Dylancyclone/thesis/defense/images/chrome_coo2XuAIJX.png

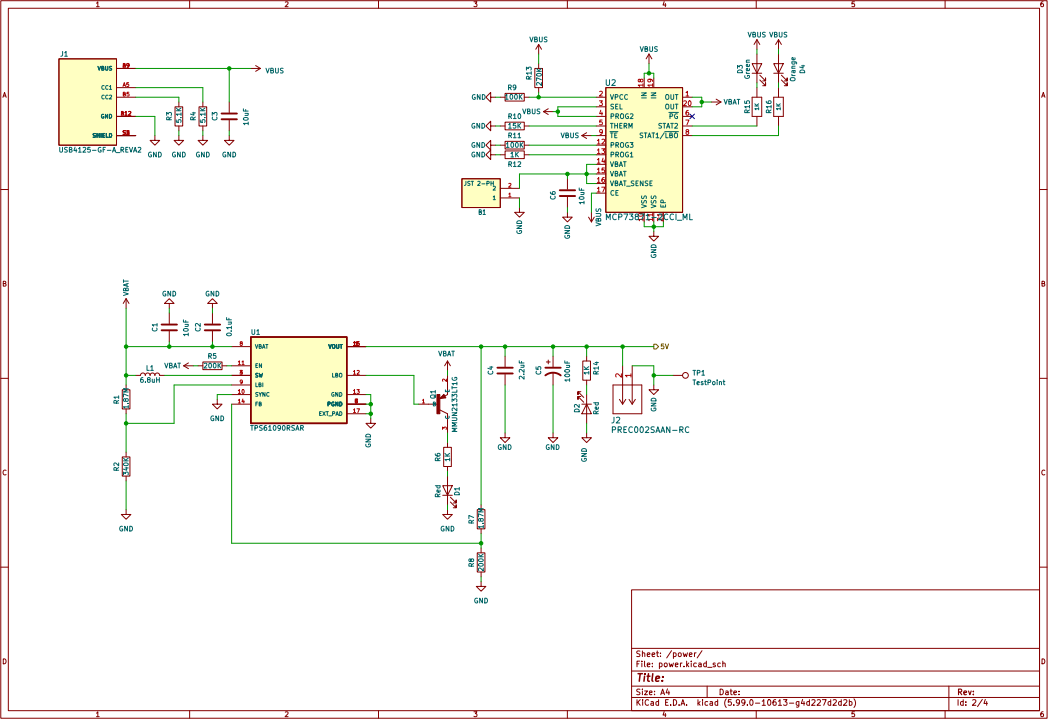
defense/images/chrome_coo2XuAIJX.png
