Dylancyclone/thesis/defense/images/colordelay.png

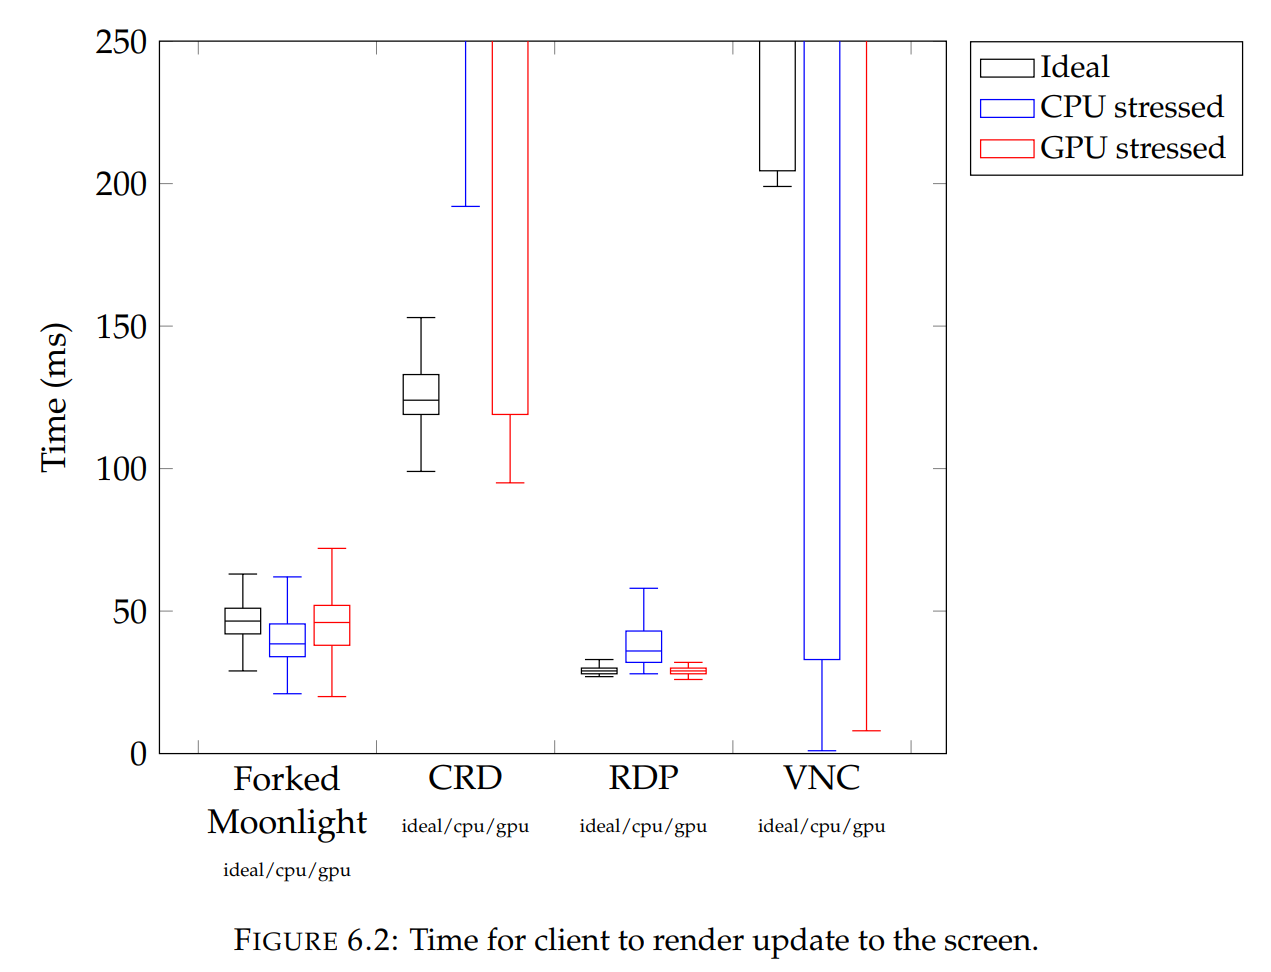
defense/images/colordelay.png
