Dylancyclone/thesis/defense/images/colordelayloss.png

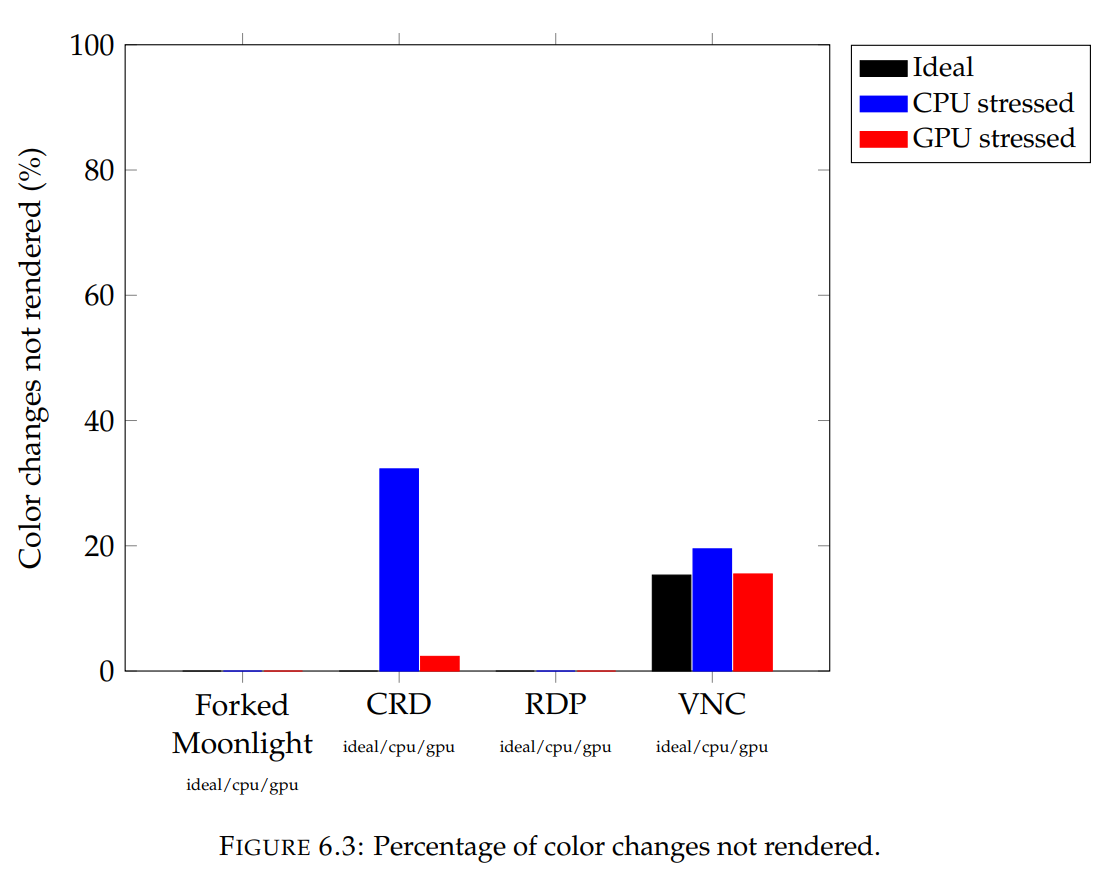
defense/images/colordelayloss.png
