Dylancyclone/thesis/defense/images/crd.png

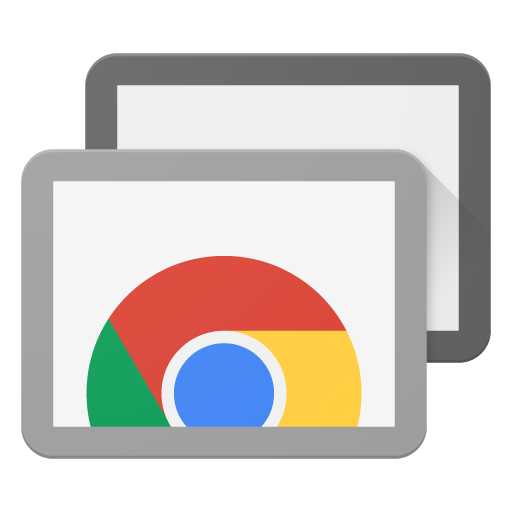
defense/images/crd.png
