Dylancyclone/thesis/defense/images/inputdelay.png

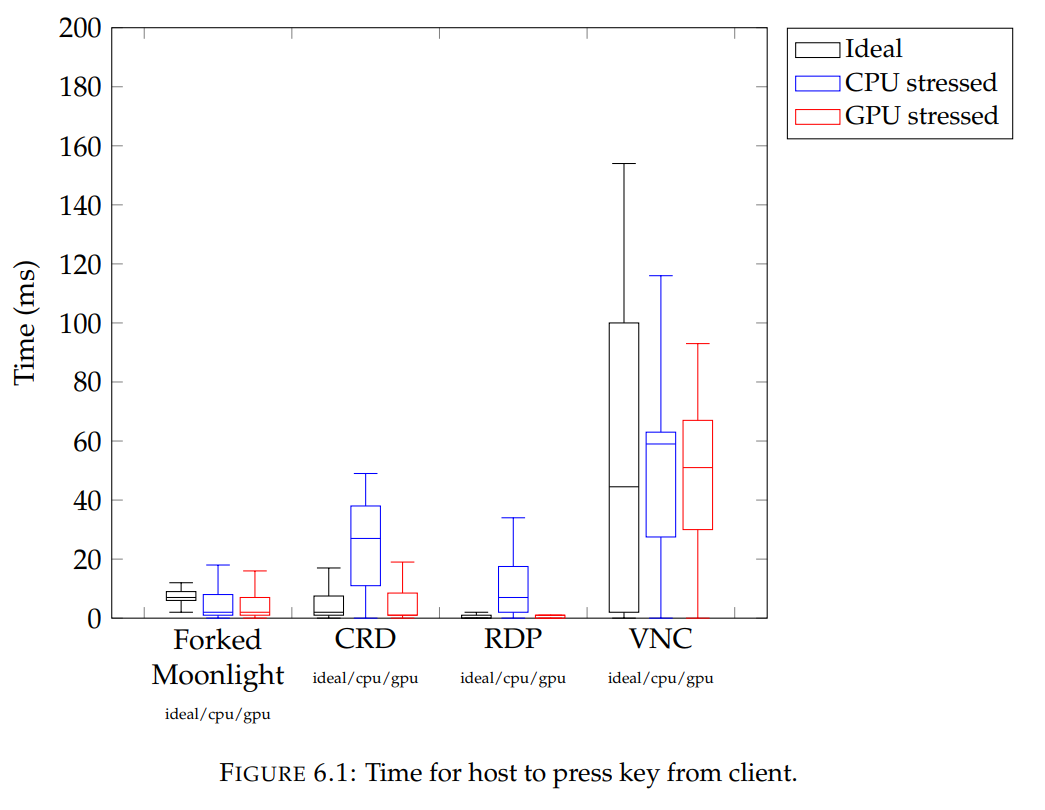
defense/images/inputdelay.png
