Dylancyclone/thesis/defense/images/moonlightstats.png

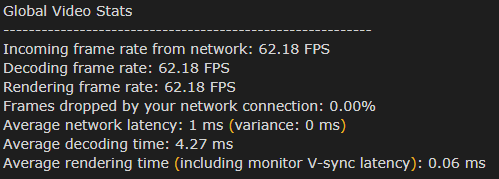
defense/images/moonlightstats.png
