Dylancyclone/thesis/defense/images/thin_client.png

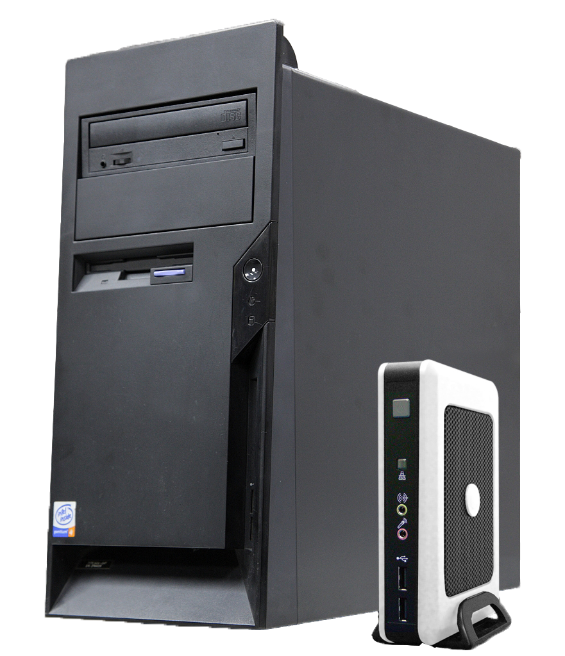
defense/images/thin_client.png
