Dylancyclone/thesis/defense/images/vnc.png

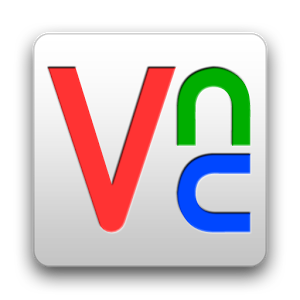
defense/images/vnc.png
