Dylancyclone/thesis/notes/rt9742.png

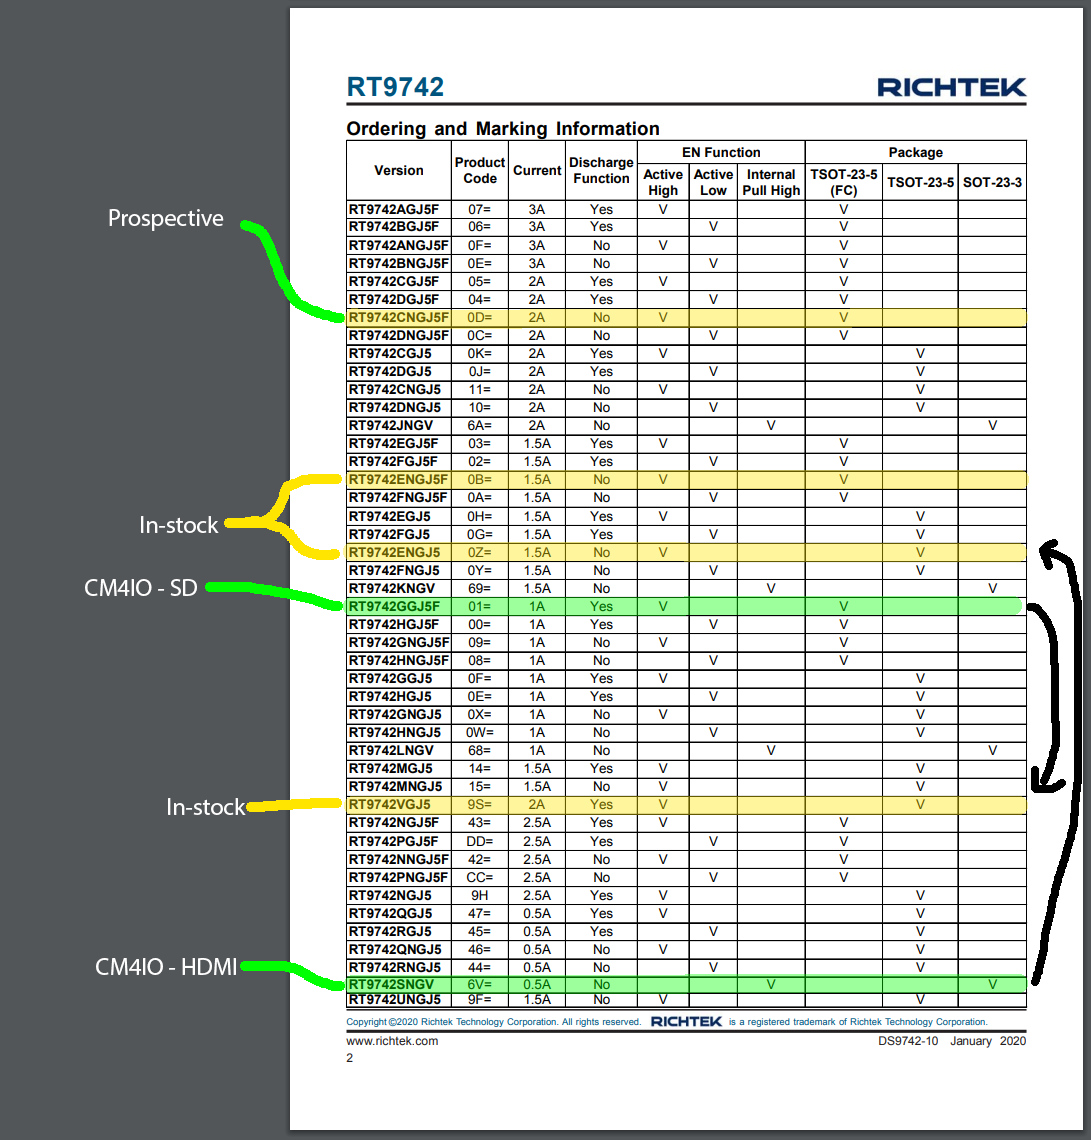
notes/rt9742.png
