Dylancyclone/thesis/paper/Figures/crd/bandwidth.png

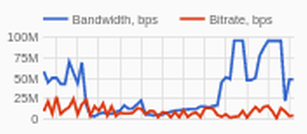
paper/Figures/crd/bandwidth.png
